lab11/monjolo/hardware/blast/rev_a/blast_pcb.png

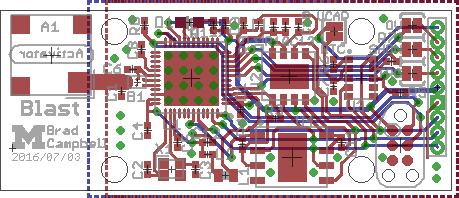
hardware/blast/rev_a/blast_pcb.png
