lab11/monjolo/hardware/breeze/rev_a/breeze_pcb.png

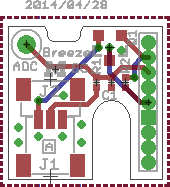
hardware/breeze/rev_a/breeze_pcb.png
