lab11/monjolo/hardware/cc_power_supply/rev_a/cc_power_supply_pcb.png

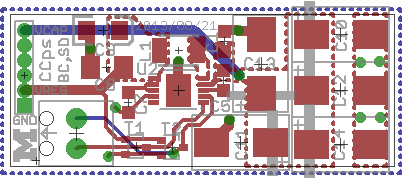
hardware/cc_power_supply/rev_a/cc_power_supply_pcb.png
