lab11/monjolo/hardware/coilcube/rev_c/coilcube_pcb.png

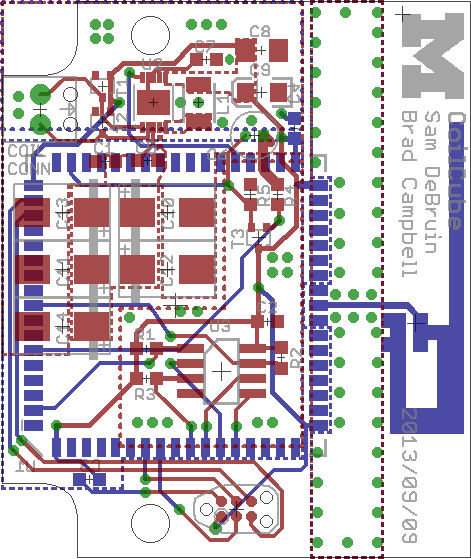
hardware/coilcube/rev_c/coilcube_pcb.png
