lab11/monjolo/hardware/impulse/rev_c/impulse_pcb.png

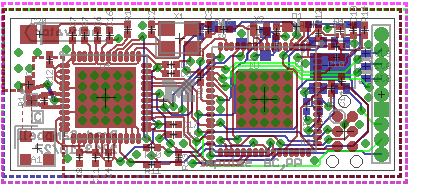
hardware/impulse/rev_c/impulse_pcb.png
