lab11/monjolo/hardware/sEHnsor/rev_a/sEHnsor.jpg

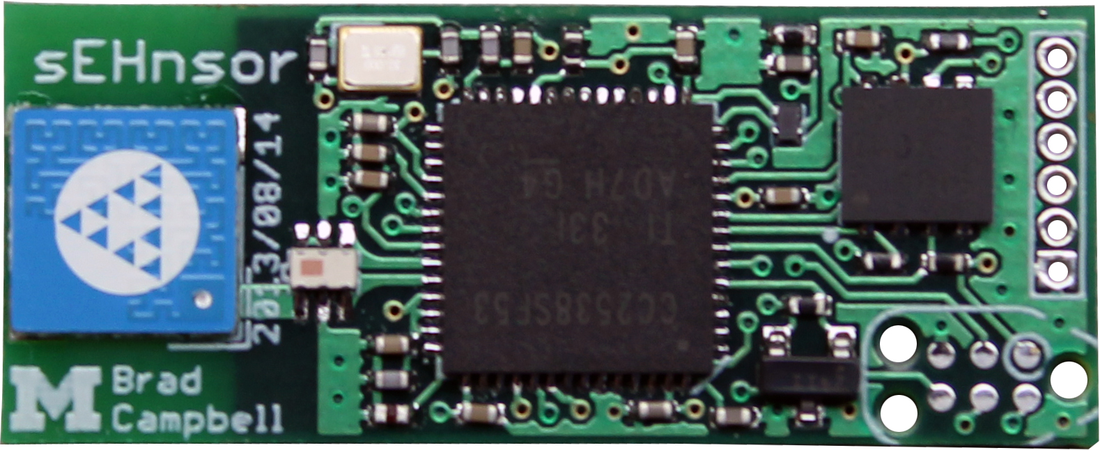
hardware/sEHnsor/rev_a/sEHnsor.jpg
