lab11/monjolo/hardware/sEHnsor/rev_a/sEHnsor_pcb.png

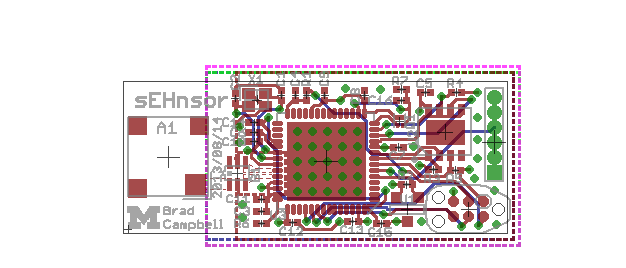
hardware/sEHnsor/rev_a/sEHnsor_pcb.png
