lab11/monjolo/media/blast_1000x405.jpg

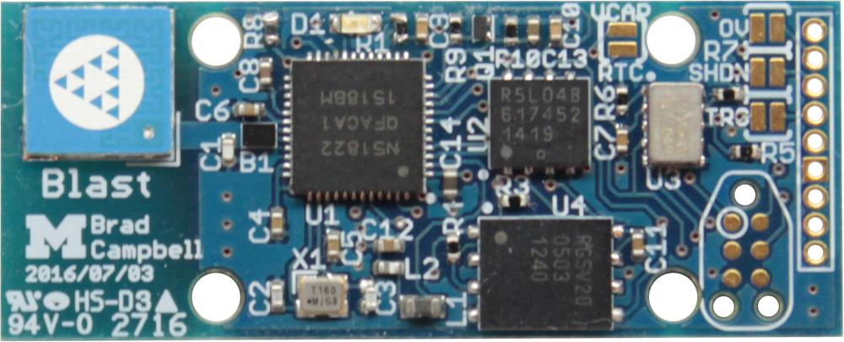
media/blast_1000x405.jpg
