lab11/monjolo/media/coilcube_case.jpg

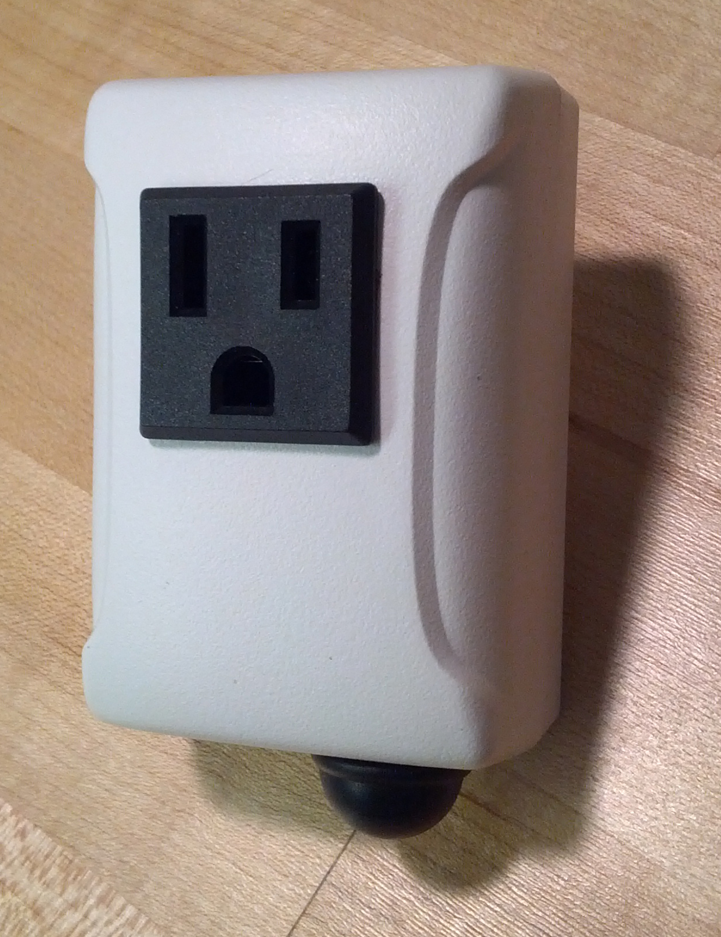
media/coilcube_case.jpg
