lab11/monjolo/media/coilcube_case_375x500.jpg

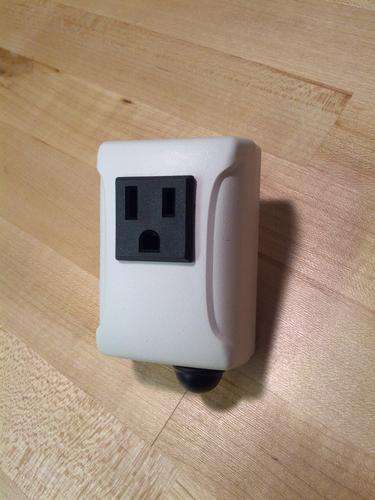
media/coilcube_case_375x500.jpg
