lab11/monjolo/media/coilcube_open.jpg

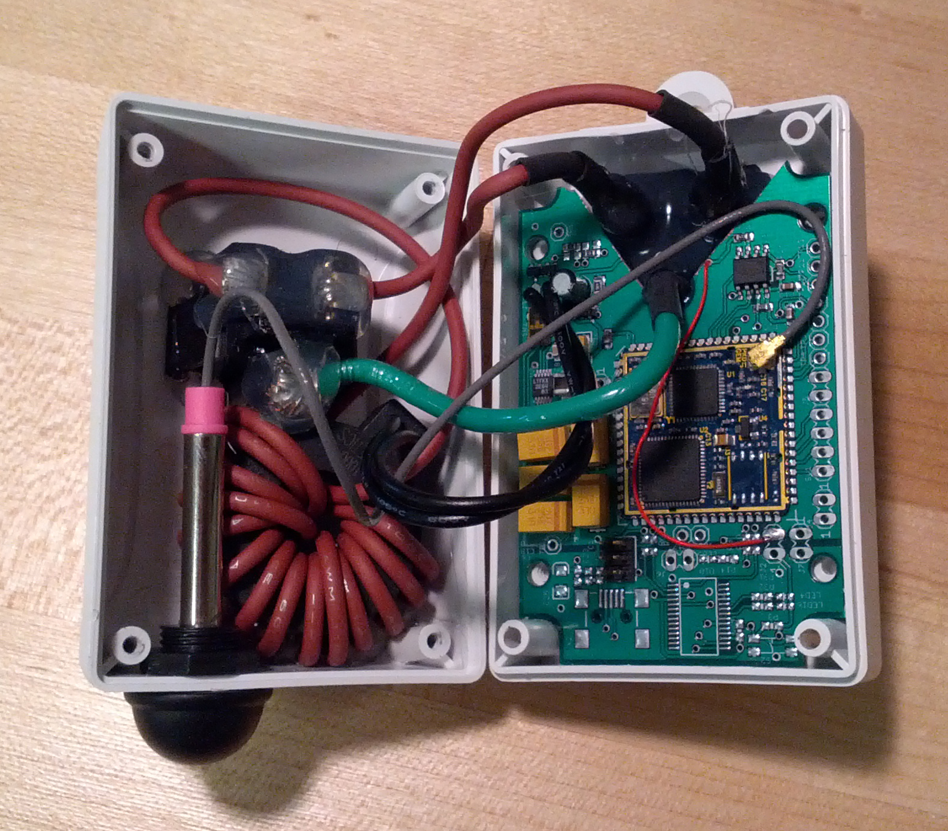
media/coilcube_open.jpg
