lab11/monjolo/media/coilcube_open_500x375.jpg

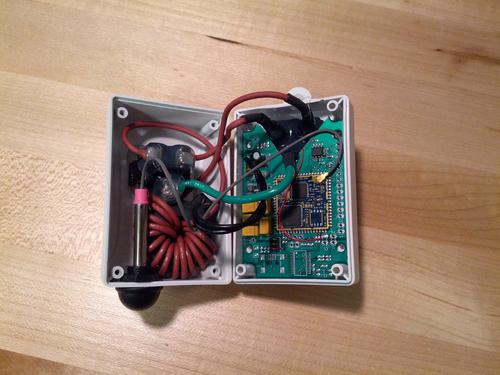
media/coilcube_open_500x375.jpg
