lab11/monjolo/media/coilcube_powerstrip.jpg

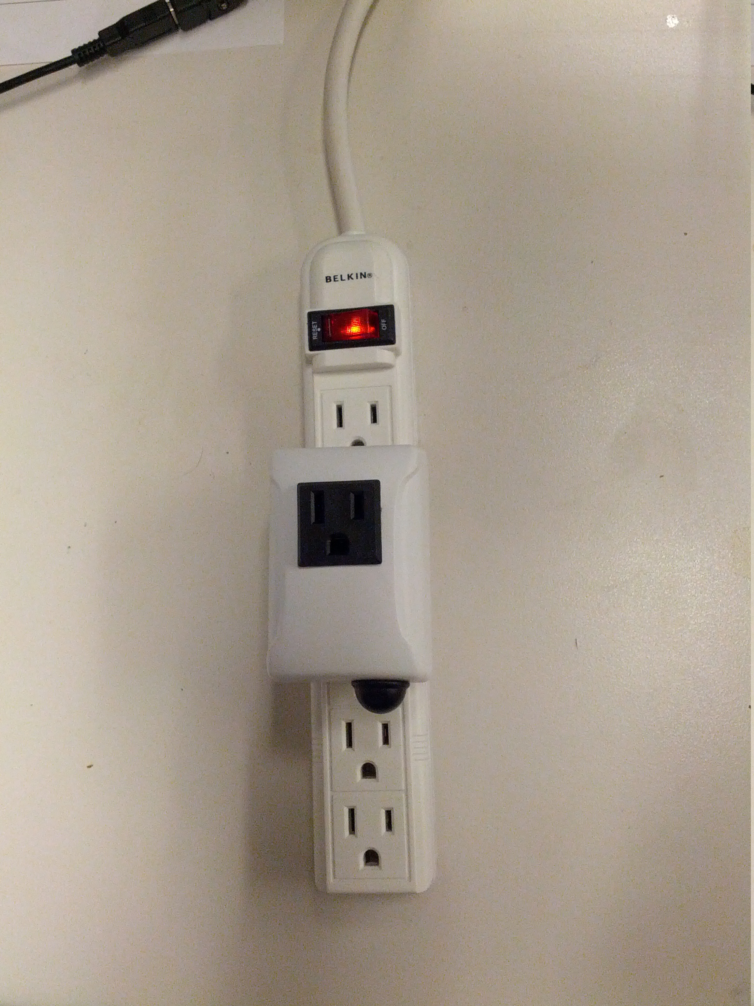
media/coilcube_powerstrip.jpg
