lab11/monjolo/media/gecko_power_supply_top_300x121.jpg

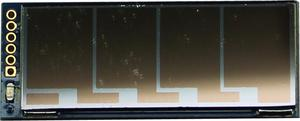
media/gecko_power_supply_top_300x121.jpg
