lab11/monjolo/media/ligeiro_1000x562.jpg

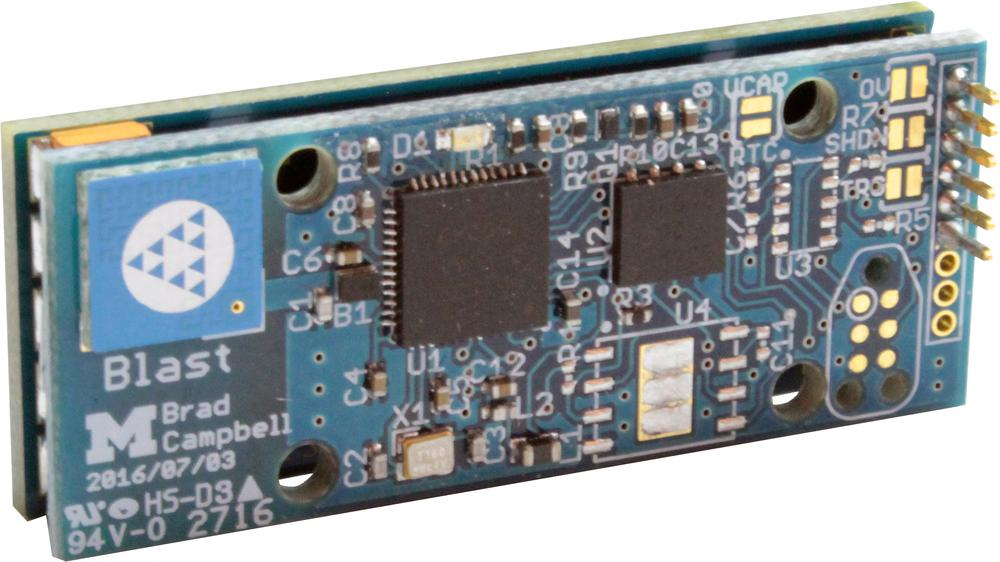
media/ligeiro_1000x562.jpg
