lab11/monjolo/media/ligeiro_case_alone_1000x724.jpg

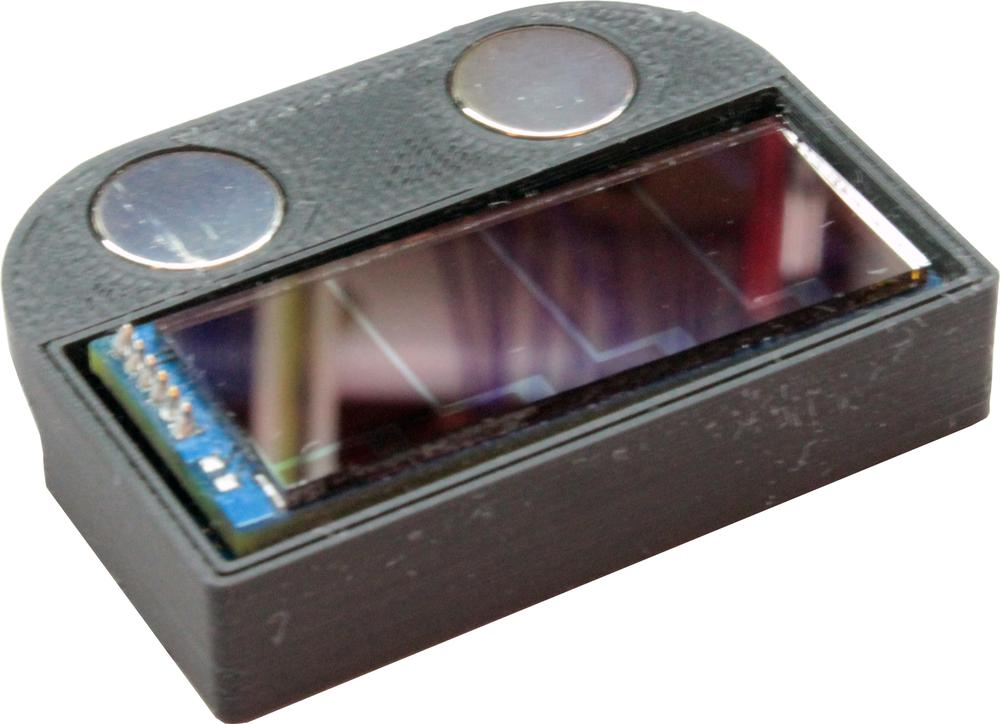
media/ligeiro_case_alone_1000x724.jpg
