lab11/monjolo/media/ligeiro_in_case_1000x1000.jpg

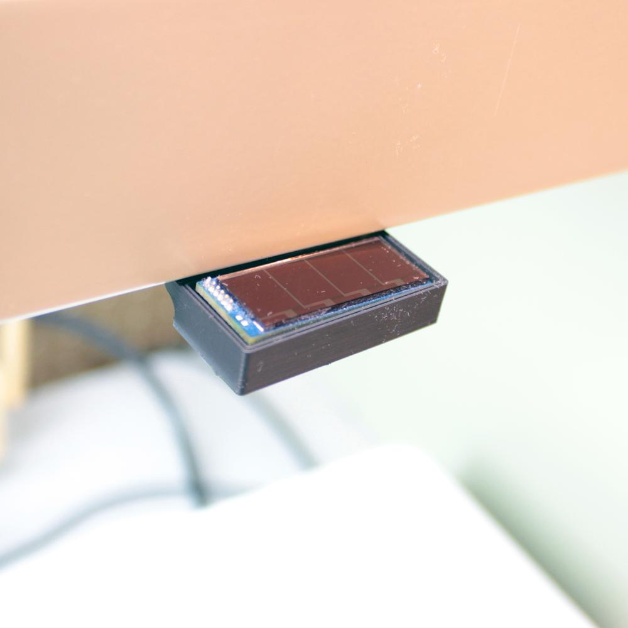
media/ligeiro_in_case_1000x1000.jpg
