lab11/monjolo/media/ligeiro_in_case_thin_1000x354.jpg

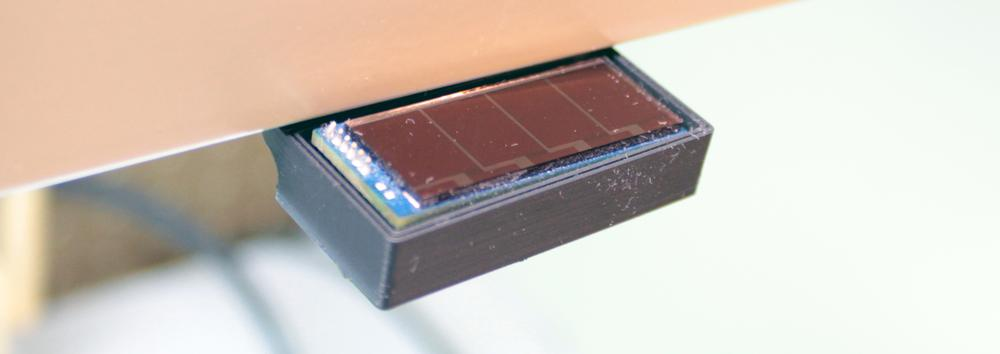
media/ligeiro_in_case_thin_1000x354.jpg
