lab11/monjolo/hardware/coilcube/rev_a/coilcube.pdf

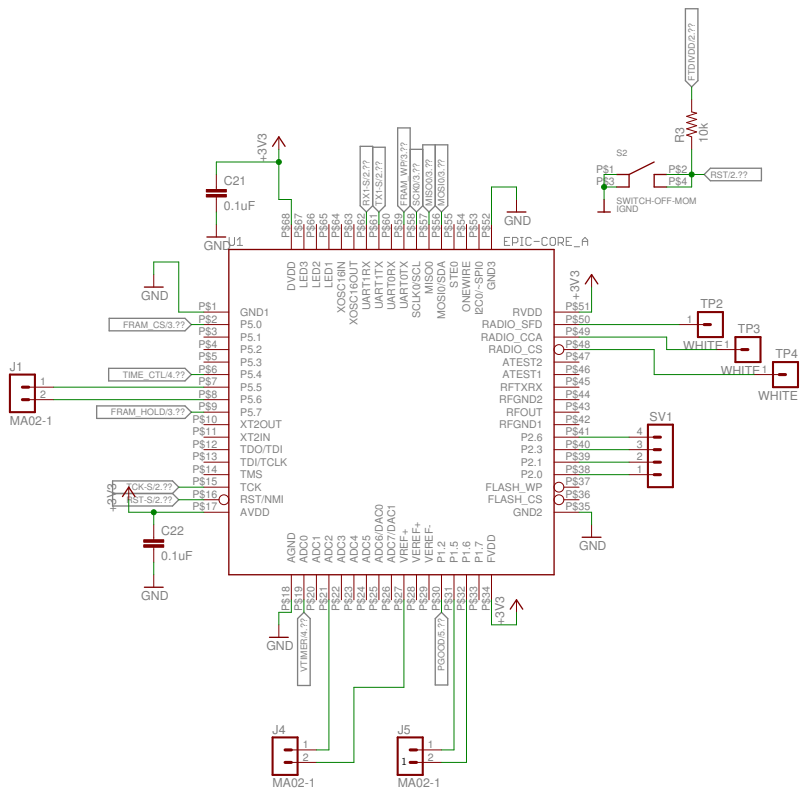
[picture p187: page 1]

C1 P$26 VREF+ P$27 VEREF+ P$28 VEREF- P$29 P1.2 P$30 P1.5 P$31 P1.6 P$32 P1.7 P$33 FVDD

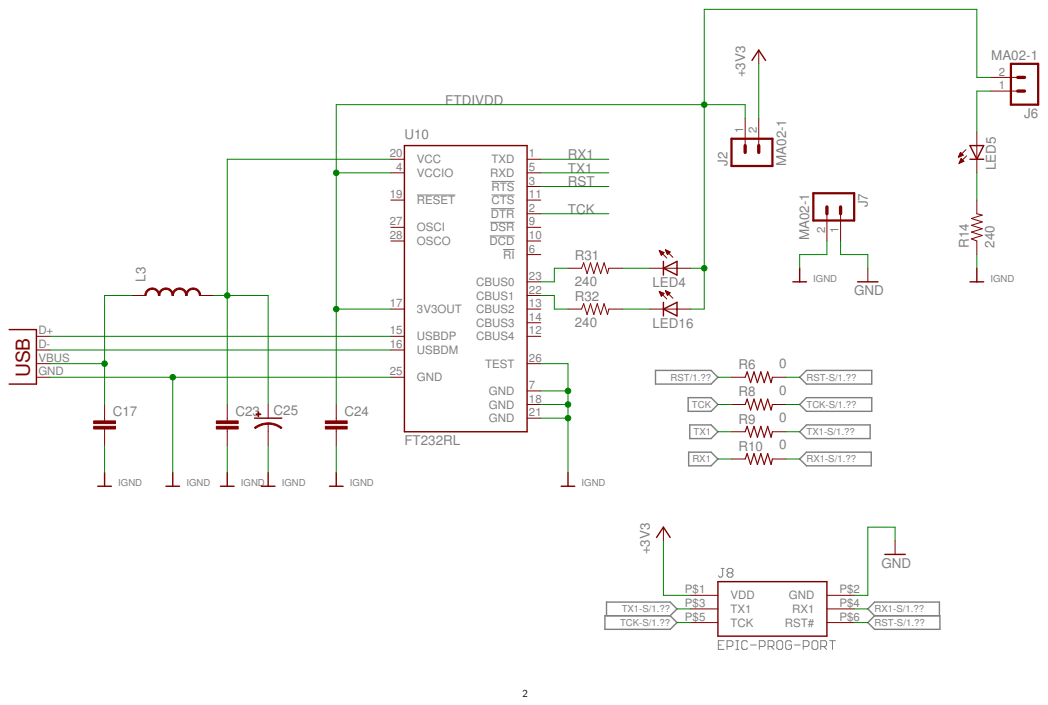
[picture p188: page 2]

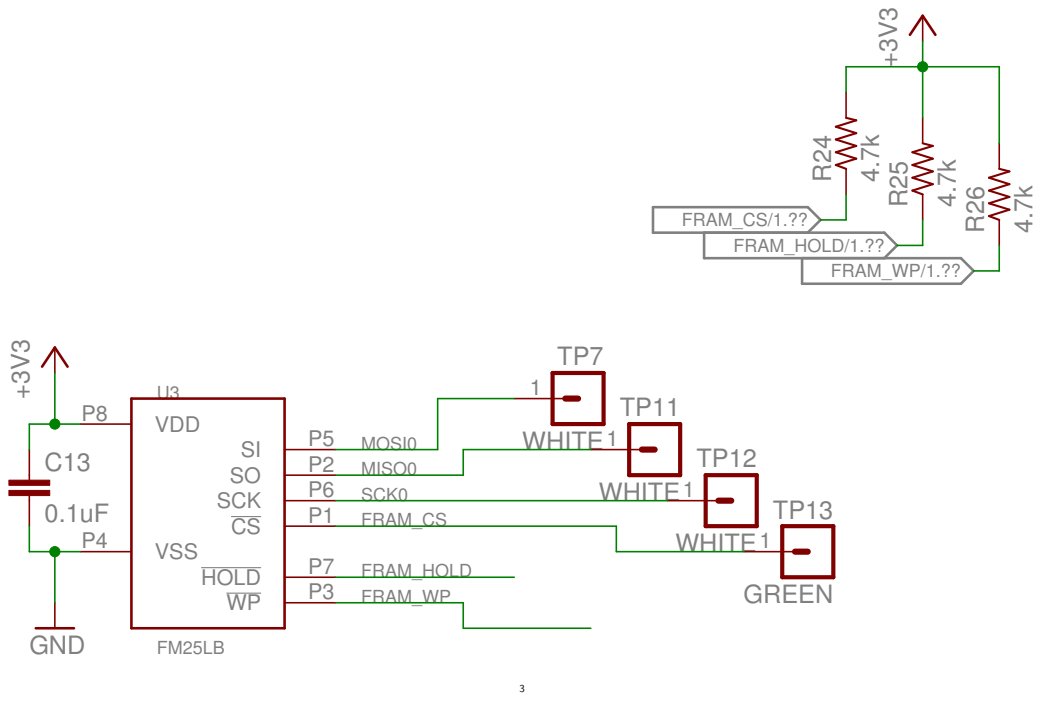
[picture p189: page 3]

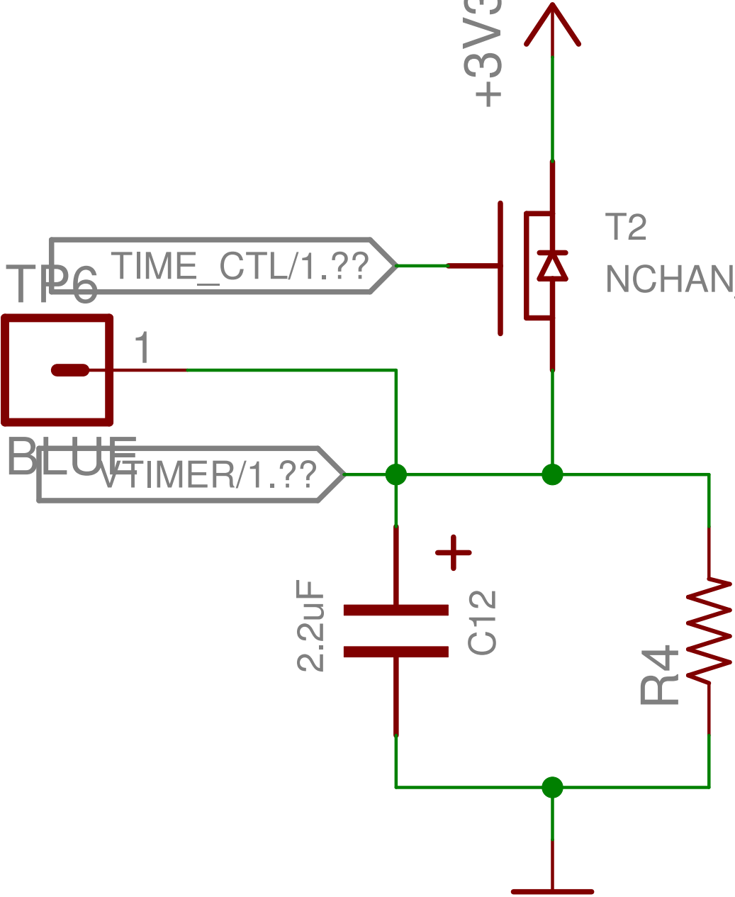
[picture p190: figure]
BLUE; VTIMER/1.??; TIME_CTL/1.??

4.7

M

# GND

# NCHAN_MOSFET

3

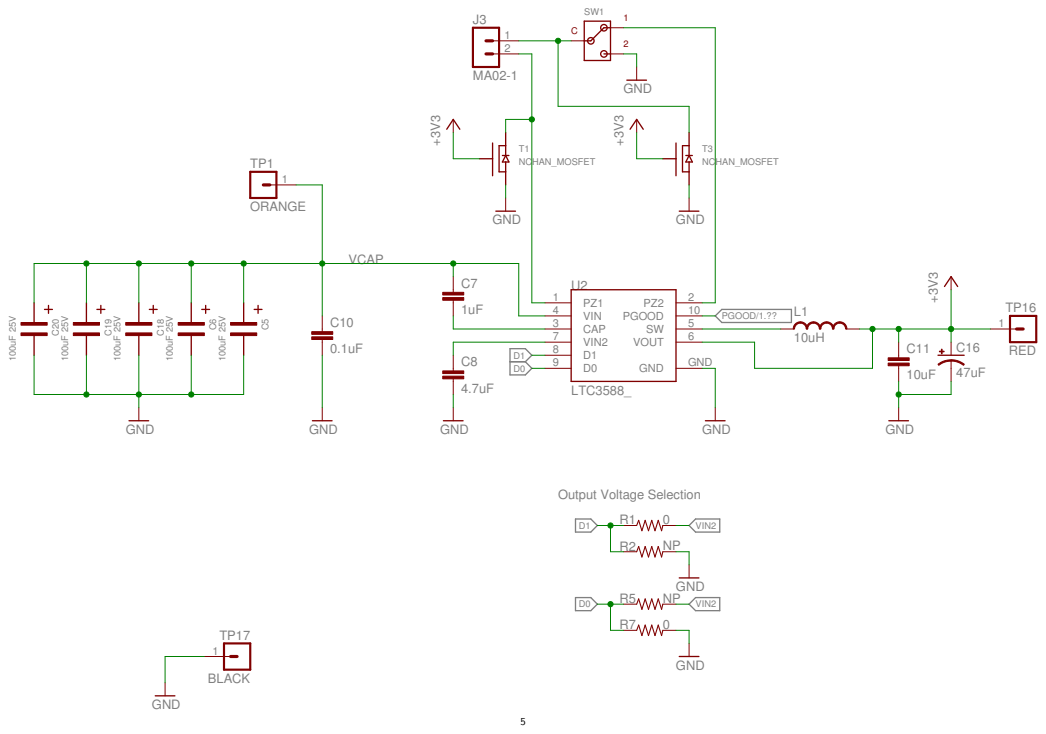
[picture p191: page 5]

Top and Bottom Layers 6 | 1 1 | 1 1 | 1 | 1 4 ¹ | 1

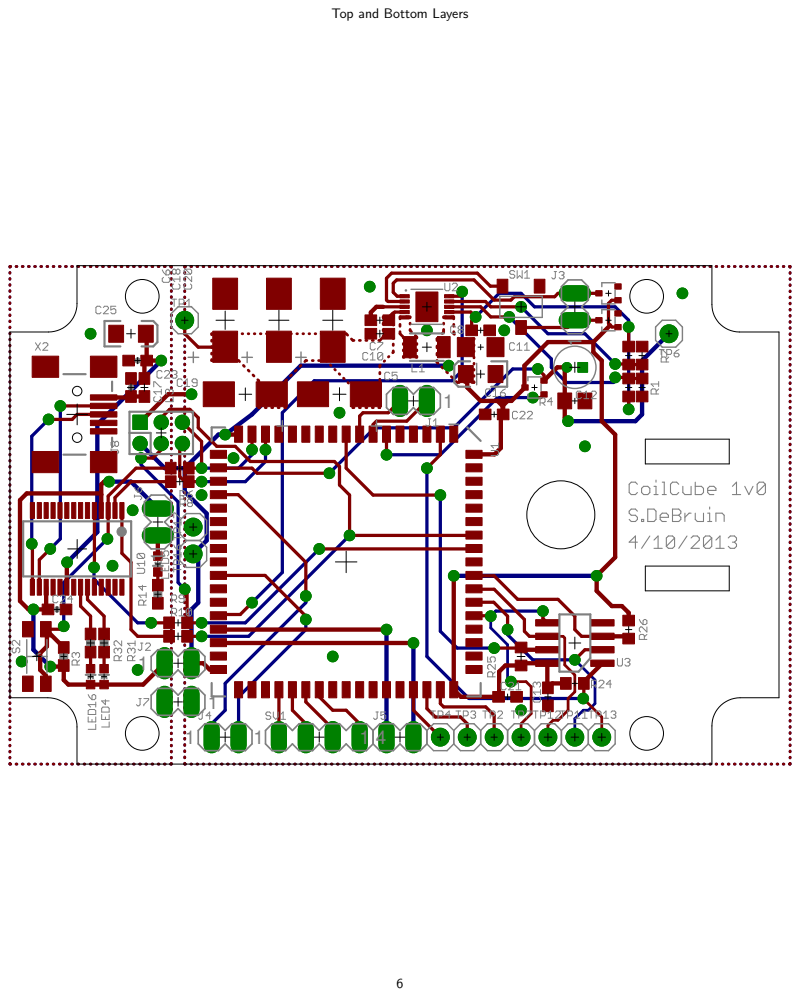
[picture p192: page 6]

Top Layer 7 | 1 1 | 1 1 | 1 | 1 4 ¹ | 1

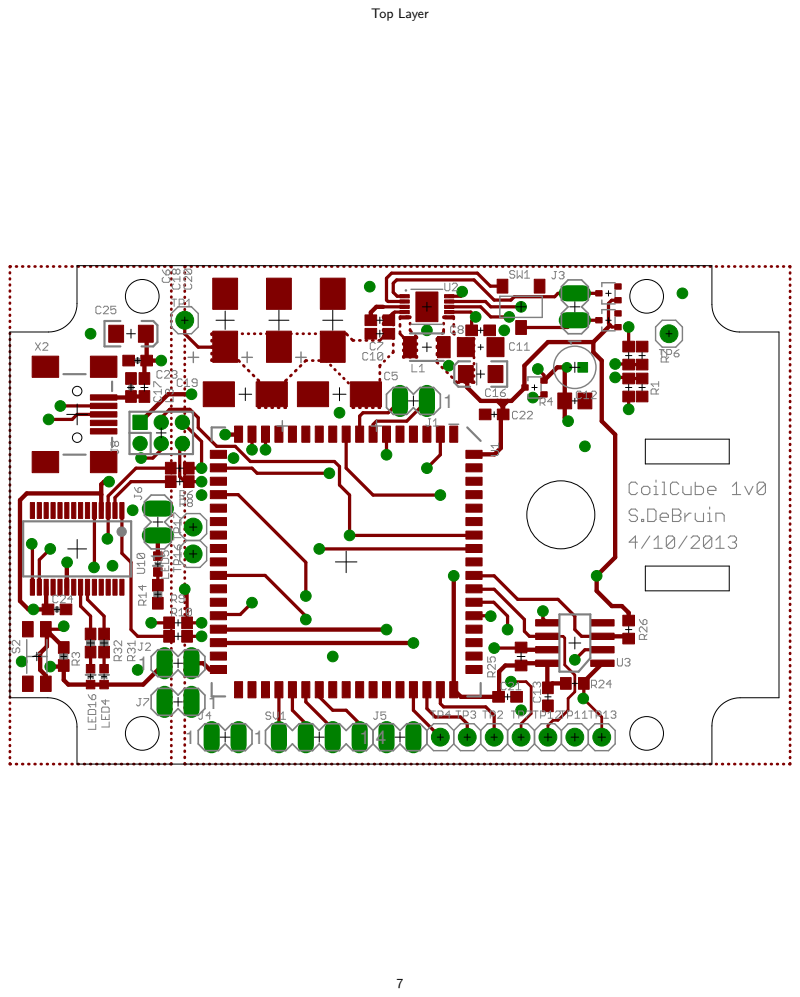
[picture p193: page 7]

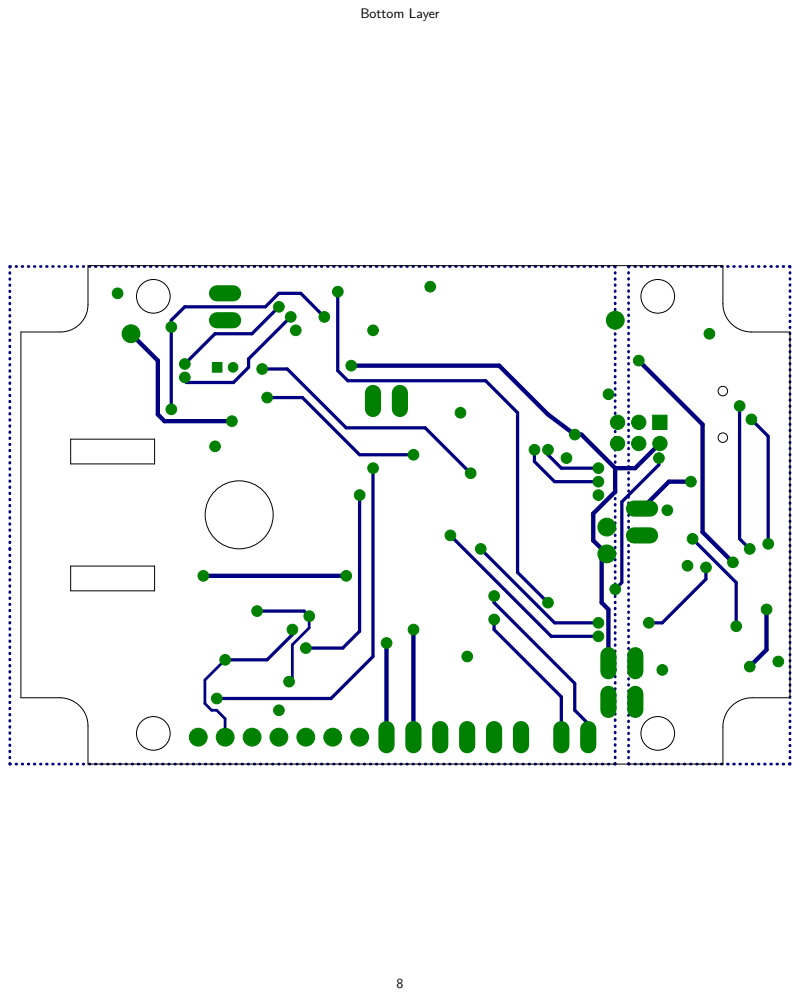
[picture p194: page 8]
Bottom Layer

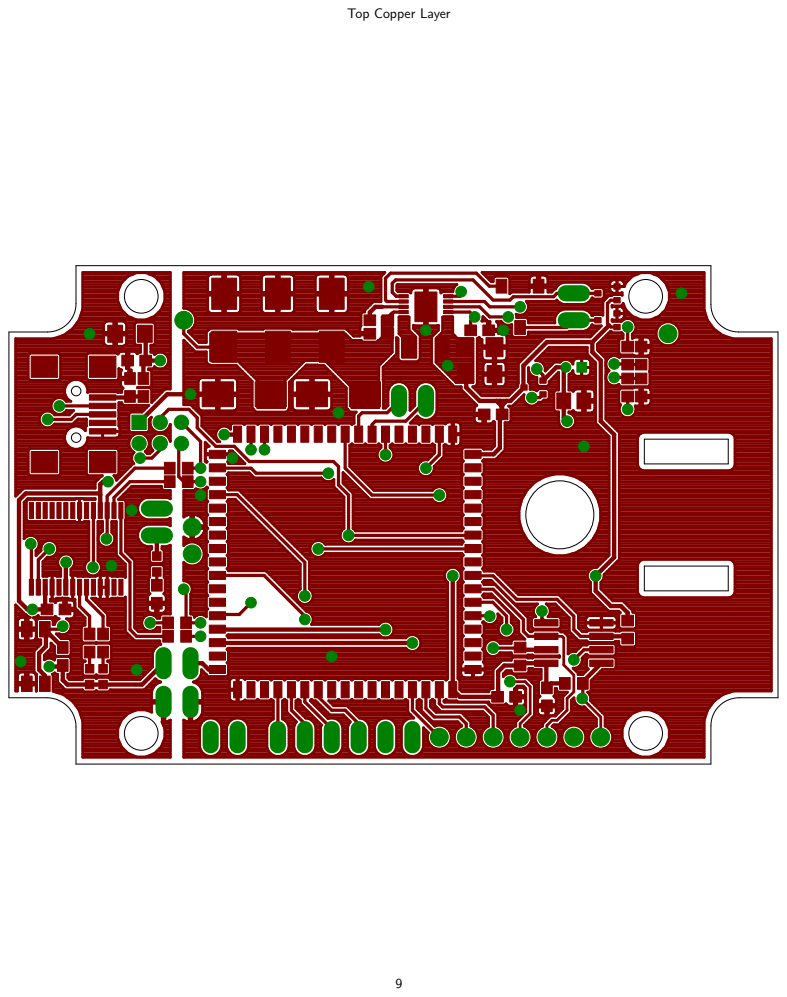
[picture p195: page 9]

Top Copper Layer

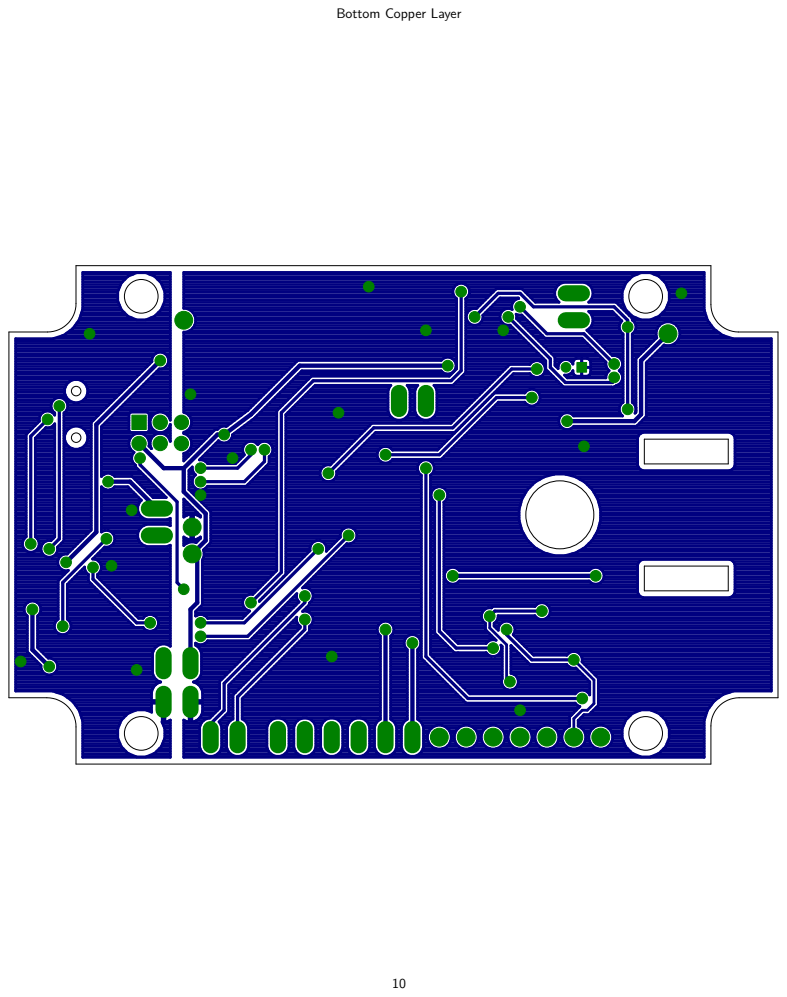
[picture p196: page 10]

Bottom Copper Layer

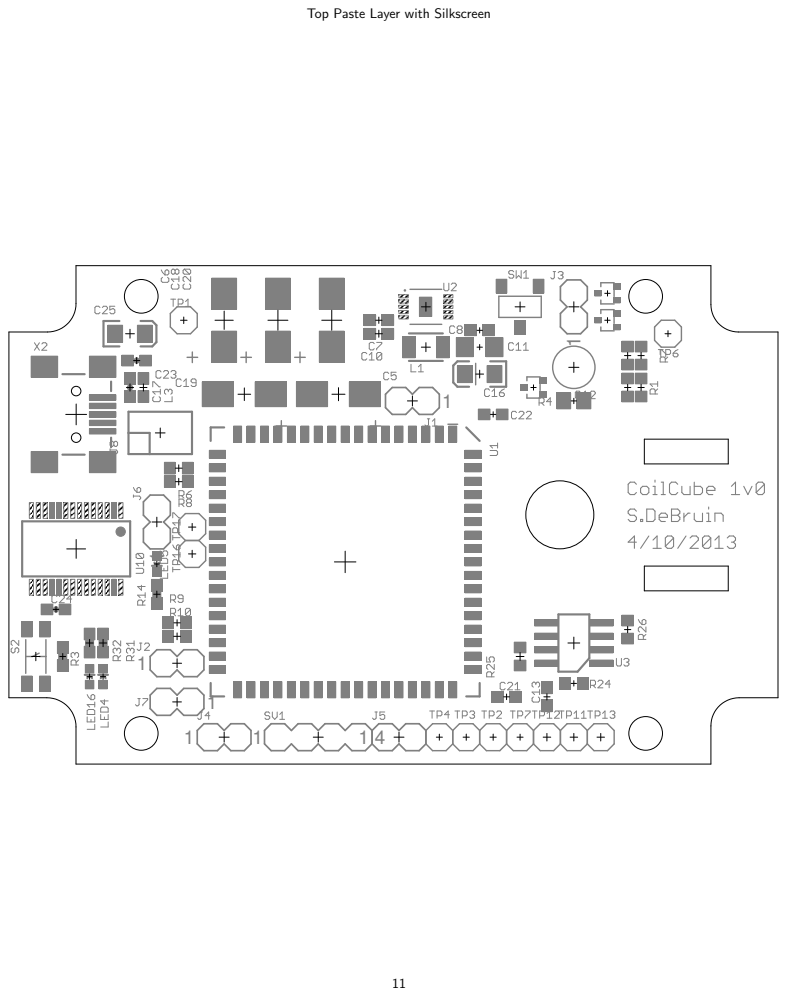
[picture p197: page 11]

Top Paste Layer with Silkscreen

Bottom Paste Layer with Silkscreen

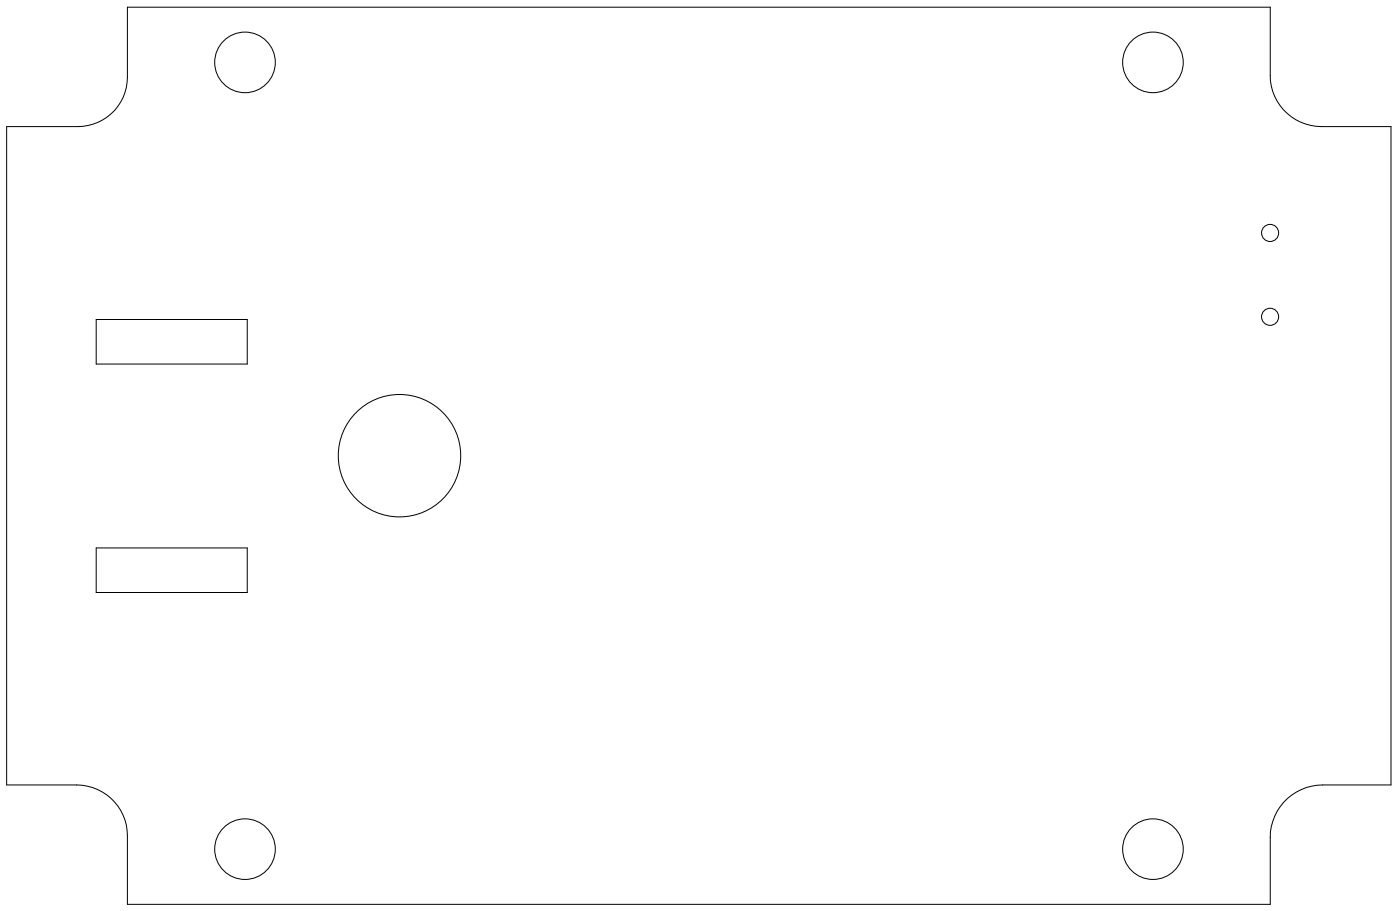
[picture p198: figure]
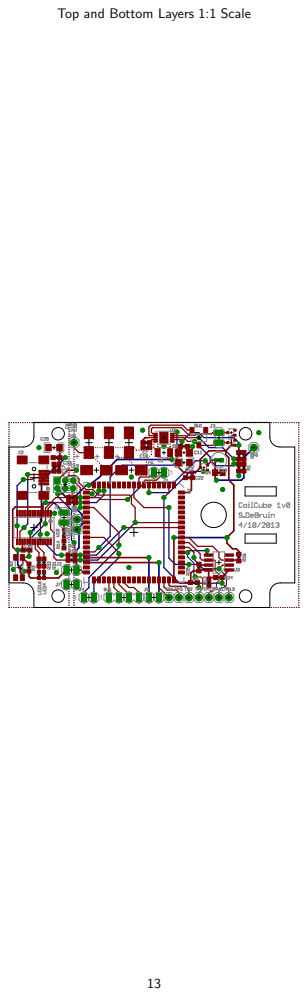
[picture p199: page 13]

Top and Bottom Layers 1:1 Scale

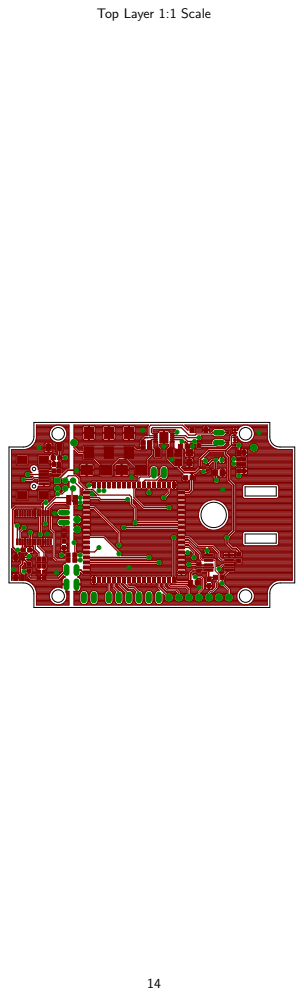
[picture p200: page 14]

Top Layer 1:1 Scale

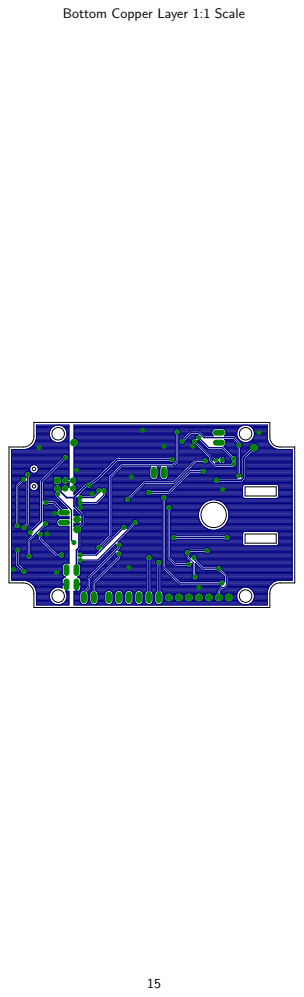
[picture p201: page 15]

Bottom Copper Layer 1:1 Scale
