lab11/monjolo/hardware/gecko_power_supply/rev_d/monjolo_d.brd

## EAGLE design hardware/gecko_power_supply/rev_d/monjolo_d.brd (2013-11-26, an earlier design)

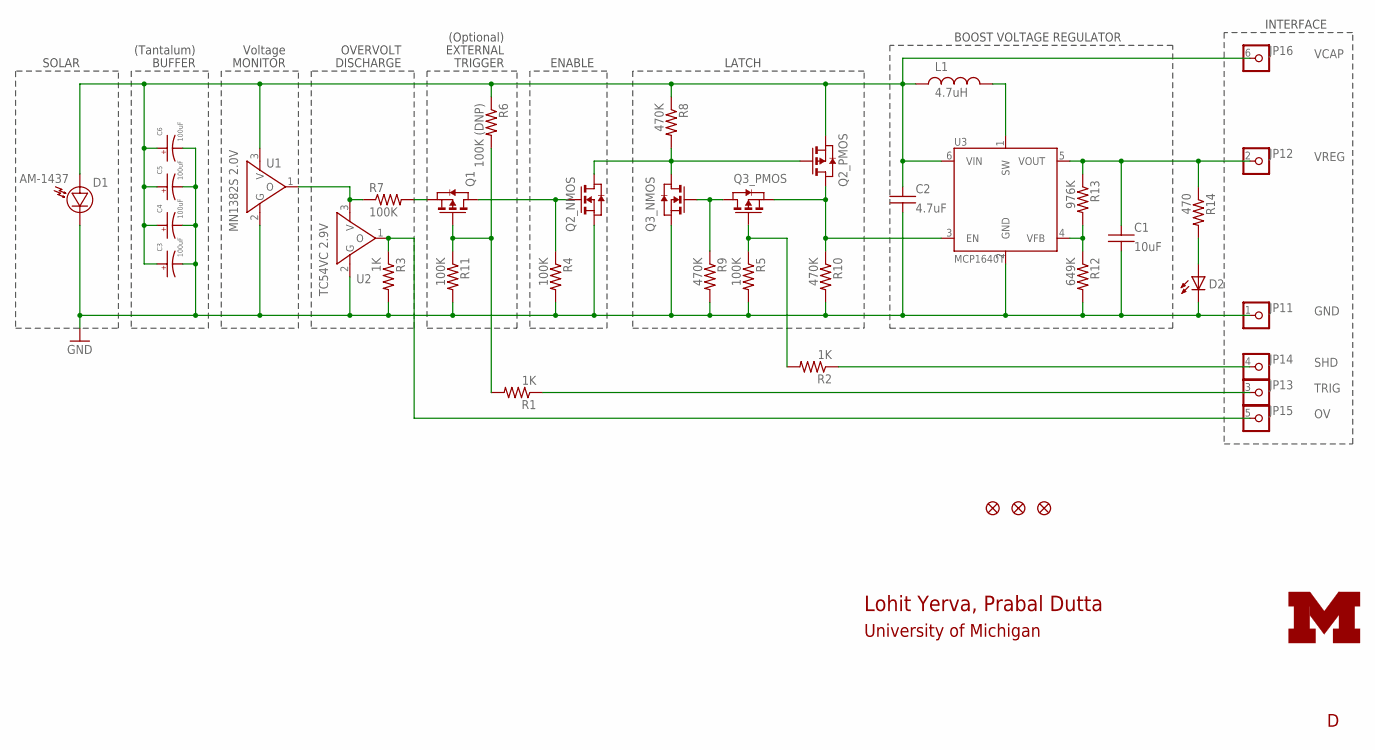
[picture p237: schematic monjolo_d.sch]

Parts:
C1: 10uF; R0603B
C2: 4.7uF; R0603B
C3, C4, C5, C6: 100uF; CAP1210
D1: AM-1437
D2: LED0603; LED-0603
JP1: PINHD6; HD6
JP2, JP3, JP4: FIDUCIAL1X2; FIDUCIAL-1X2
L1: 4.7uH; L2828
Q1: PMOSSOT23; SOT-23
Q2, Q3: DUAL_MOSFET_NP; TSOP-6
R1, R2, R3: 1K; R0603B
R4, R5, R7, R11: 100K; R0603B
R6: 100K (DNP); R0603B
R8, R9, R10: 470K; R0603B
R12: 649K; R0603B
R13: 976K; R0603B
R14: 470; R0603B
U1: MN1382S 2.0V; MINI-3DC
U2: TC54VC 2.9V; MINI-3DC
U3: MCP1640T; SOT-23-6
U$1: UMICH_SOLID_SMALL; UMICH_SOLID_75MIL

Connections:
GND: C1.2, C2.2, C3.ANODE, C4.ANODE, C5.ANODE, C6.ANODE, D1.- (C), D2.C, JP1.1, Q2.5 (S), Q3.5 (S), R3.2, R4.2, R5.2, R9.2, R10.2, R11.2, R12.2, U1.2 (G), U2.2 (G), U3.2 (GND)
unnamed: R12.1, R13.2, U3.4 (VFB)
unnamed: Q1.2 (S), R7.2
unnamed: JP1.3, R1.1
unnamed: L1.2, U3.1 (SW)
unnamed: D2.A, R14.2
unnamed: Q3.1 (G), Q3.4 (D), R9.1
unnamed: Q1.1 (D), Q2.1 (G), R4.1
unnamed: JP1.4, R2.1
unnamed: Q2.3 (G), Q2.6 (D), Q3.6 (D), R8.2
unnamed: Q3.3 (G), R2.2, R5.1
unnamed: JP1.5, R3.1, U2.1 (O)
unnamed: R7.1, U1.1 (O), U2.3 (V)
unnamed: Q1.3 (G), R1.2, R6.2, R11.1
unnamed: Q2.4 (D), Q3.2 (S), R10.1, U3.3 (EN)
VCAP: C2.1, C3.CATHODE, C4.CATHODE, C5.CATHODE, C6.CATHODE, D1.+ (A), JP1.6, L1.1, Q2.2 (S), R6.1, R8.1, U1.3 (V), U3.6 (VIN)
VREG: C1.1, JP1.2, R13.1, R14.1, U3.5 (VOUT)

Notes on the sheet:
Lohit Yerva, Prabal Dutta
VCAP
VREG
GND
SHD
TRIG
University of Michigan
SOLAR
(Tantalum)
BUFFER
Voltage
MONITOR
OVERVOLT
DISCHARGE
EXTERNAL
TRIGGER
(Optional)
ENABLE
LATCH
BOOST VOLTAGE REGULATOR
INTERFACE

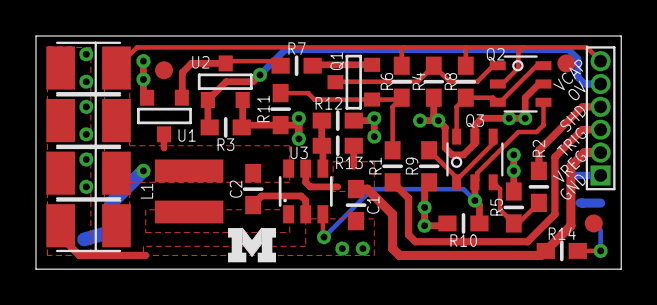
[picture p238: board monjolo_d.brd from above]

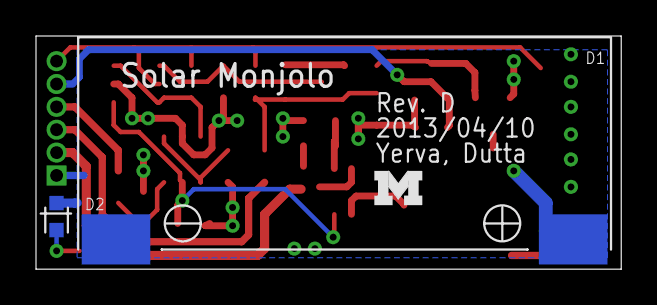
[picture p239: board monjolo_d.brd from below]

Board: 2 copper layers, 32.5 x 13.0 mm, 35 parts (3 on the bottom side), 17 nets.

Other parts of the board:
U$3: UMICH_SOLID_SMALL; UMICH_SOLID_75MIL
