lab11/monjolo/hardware/myth/rev_a/myth.brd

## EAGLE design hardware/myth/rev_a/myth.brd (2014-04-28)

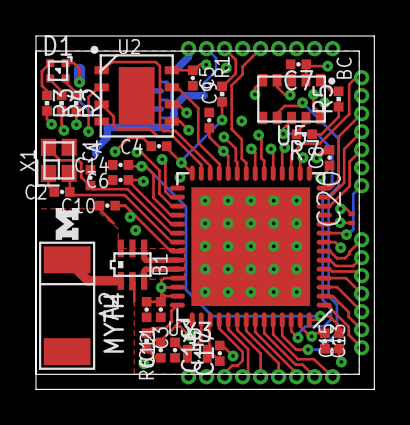
[picture p240: board myth.brd from above]

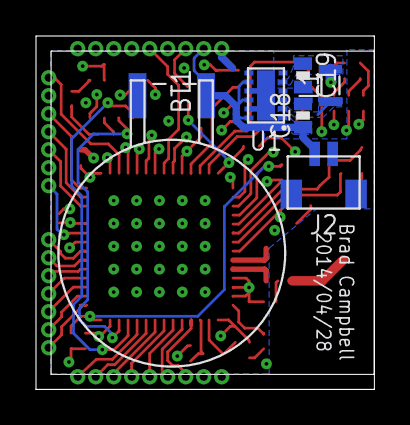
[picture p241: board myth.brd from below]

Board: 4 copper layers, 18.8 x 19.6 mm, 41 parts (6 on the bottom side), 55 nets.

Parts:
A2: FRACTUS-2.4GHZ-FR05-S1-N-0-102; FRACTUS-ANTENNA-FR05-S1-N-0-102
B1: 2450BM15A0002; 2450BM
BT1: ML-1220/F1AN; ML-1220/F1BN
C1, C2: 12pF; 0402_CAP
C3: 220pF; 0402_CAP
C4: 1nF; 0402_CAP
C5, C6, C8, C9, C10, C11, C12: 0.1uF; 0402_CAP
C7: 10nF; 0402_CAP
C13, C14, C15: 1uF; 0402_CAP
C16, C17: 22pF; 0402_CAP
C18, C19: 10uF; 0603_CAP
C20: 0.1uF; C0201
D1: SML-LX0404SIUPGUSB; 1MM_SQ_4PAD
J1: EPIC2-HEADER2
J2: SH_MALE_2/1MM; SH-1X2/1MM
L1: 2.2; MIPSZ201D
LOGO1: UMICH_SOLID_TINY; UMICH_SOLID_50MIL
R1: 2.2k; 0402_RES
R2, R3, R4: 1k; 0402_RES
R5, R7: 10k; 0402_RES
R6: 56k; 0402_RES
U1: TPS62740; R-PWSON-12
U2: FM25LBTDFN-8; TDFN-8
U3: CC2538; S-PVQFN-N56
U5: RV-3049-C3; MICRO-CRYSTAL-C3
X1: EPSON-FA-128; FA-128
X3: ABS05-32.768KHZ-T; ABS05

Connections:
!FRAM_CS: U2.1, U3.26
!FRAM_HOLD: U2.7, U3.25
!FRAM_WP: U2.3, U3.27
!RESET: J1.30, R1.1
!RTC_INT: U3.53, U5.7
ADC3: J1.25, U3.19
ADC4: J1.26, U3.20
ADC5: J1.27, U3.21
ADC6: J1.28, U3.22
ADC7: J1.29, U3.23
ANTENNA: A2.1, B1.1
B3: J1.9, U3.52
B4: J1.8, U3.51
B5: J1.7, U3.50
B6: J1.6, U3.49
BATTERY: BT1.POS, C18.1, J1.31, J2.2, U1.1, U1.8, U1.10, U1.12
BOOTLOADER_CTRL: J1.24, U3.18
BOOTLOADER_RX: J1.22, U3.16
BOOTLOADER_TX: J1.23, U3.17
C0: J1.21, U3.14
C1: J1.20, U3.13
C2: J1.19, U3.12
DGND_USB: J1.10, U3.1
DVDD_USB: J1.13, U3.4
GND: B1.2, B1.5, B1.6, BT1.NEG, C1.2, C2.2, C3.2, C4.2, C5.2, C6.2, C7.2, C8.2, C9.2, C10.2, C11.2, C12.2, C13.2, C14.2, C15.2, C16.2, C17.2, C18.2, C19.2, C20.2, J1.32, J2.1, R5.1, R6.2, R7.1, U1.3, U1.4, U1.9, U1.11, U1.NC, U2.4, U3.VSS_QFN, U5.6, X1.2, X1.4
I2C_SCL: J1.17, U3.9
I2C_SDA: J1.18, U3.8
LED_BLUE: R4.2, U3.30
LED_GREEN: R3.2, U3.31
LED_RED: R2.2, U3.29
unnamed: C4.1, R1.2, U3.28
unnamed: L1.1, U1.2
unnamed: C16.1, U3.44, X3.A
unnamed: D1.2, R2.1
unnamed: R6.1, U3.42
unnamed: C1.1, U3.34, X1.1
unnamed: C2.1, U3.35, X1.3
unnamed: D1.4, R3.1
unnamed: D1.3, R4.1
unnamed: C17.1, U3.45, X3.B
unnamed: R7.2, U5.9
unnamed: C14.1, C15.1, U3.32, U3.56
unnamed: R5.2, U5.1
RF_N: B1.3, U3.38
RF_P: B1.4, U3.37
RTC_CE: U3.54, U5.8
SPI_MISO: J1.14, U2.2, U3.5, U5.5
SPI_MOSI: J1.15, U2.5, U3.6, U5.10
SPI_SCK: J1.16, U2.6, U3.7, U5.4
TCK: J1.4, U3.47
TDO: J1.5, U3.48
TMS: J1.3, U3.46
USB_N: J1.12, U3.3
USB_P: J1.11, U3.2
VCC: C3.1, C5.1, C6.1, C7.1, C8.1, C9.1, C10.1, C11.1, C12.1, C13.1, C19.1, C20.1, D1.1, J1.1, L1.2, U1.5, U2.8, U3.10, U3.15, U3.24, U3.33, U3.36, U3.39, U3.40, U3.41, U3.43, U3.55, U5.2
