lab11/monjolo/hardware/bigben/rev_a/bigben.sch

## EAGLE design hardware/bigben/rev_a/bigben.sch (2014-05-19)

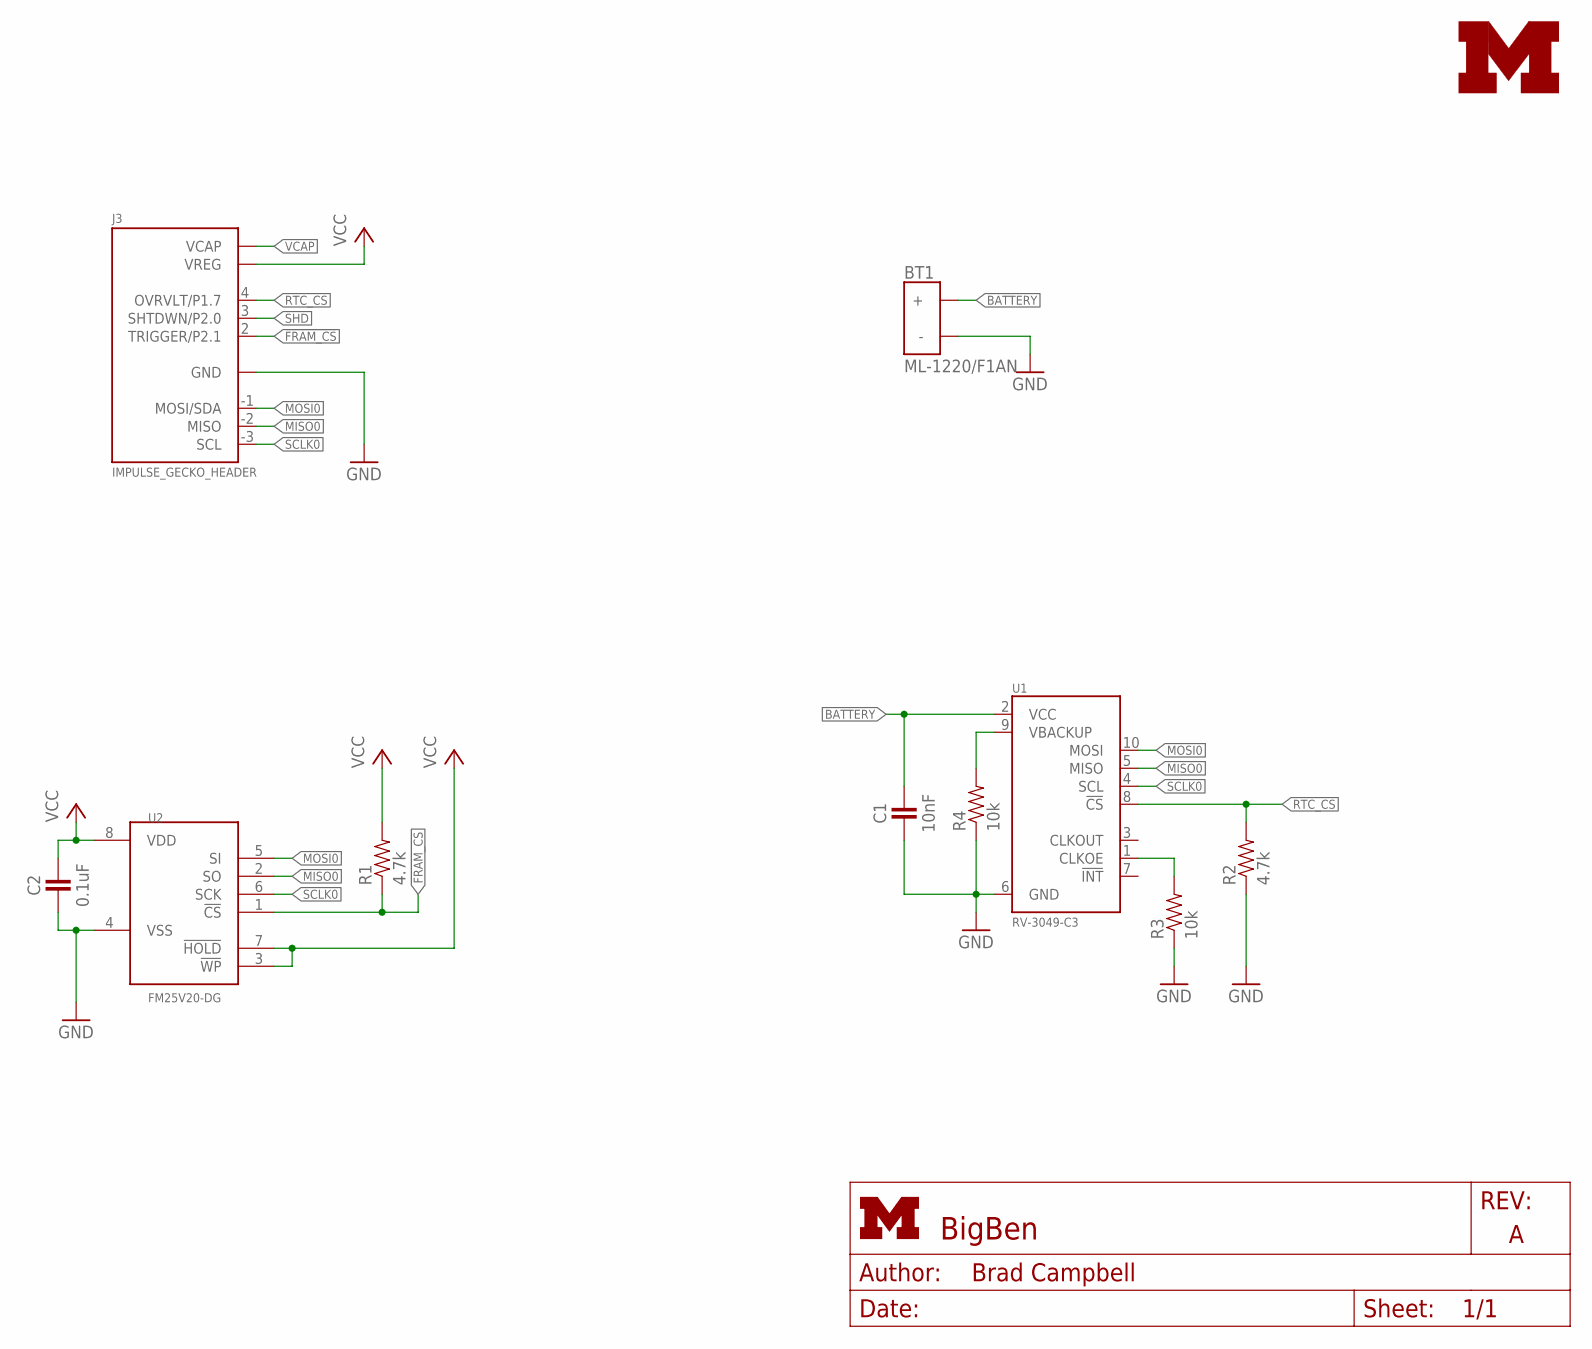
[picture p242: schematic bigben.sch]

Parts:
BT1: ML-1220/F1AN; ML-1220/F1BN
C1: 10nF; 0402_CAP
C2: 0.1uF; 0402_CAP
J3: IMPULSE_GECKO_HEADER; HEADER1X9/0.05IN
LOGO1: UMICH_SOLID_TINY; UMICH_SOLID_50MIL
R1, R2: 4.7k; 0402_RES
R3, R4: 10k; 0402_RES
U1: RV-3049-C3; MICRO-CRYSTAL-C3
U2: FM25V20-DG; TDFN-8/6MM

Connections:
!FRAM_CS: J3.2 (TRIGGER/P2.1), R1.1, U2.1 (!CS)
BATTERY: BT1.POS (+), C1.1, U1.2 (VCC)
GND: BT1.NEG (-), C1.2, C2.2, J3.0 (GND), R2.1, R3.1, R4.1, U1.6 (GND), U2.4 (VSS)
MISO0: J3.-2 (MISO), U1.5 (MISO), U2.2 (SO)
MOSI0: J3.-1 (MOSI/SDA), U1.10 (MOSI), U2.5 (SI)
unnamed: R4.2, U1.9 (VBACKUP)
unnamed: R3.2, U1.1 (CLKOE)
RTC_CS: J3.4 (OVRVLT/P1.7), R2.2, U1.8 (!CS)
SCLK0: J3.-3 (SCL), U1.4 (SCL), U2.6 (SCK)
SHD: J3.3 (SHTDWN/P2.0)
VCAP: J3.5 (VCAP)
VCC: C2.1, J3.1 (VREG), R1.2, U2.3 (!WP), U2.7 (!HOLD), U2.8 (VDD)
