lab11/monjolo/hardware/epic2/rev_a/epic2.sch

## EAGLE design hardware/epic2/rev_a/epic2.sch (2014-03-24)

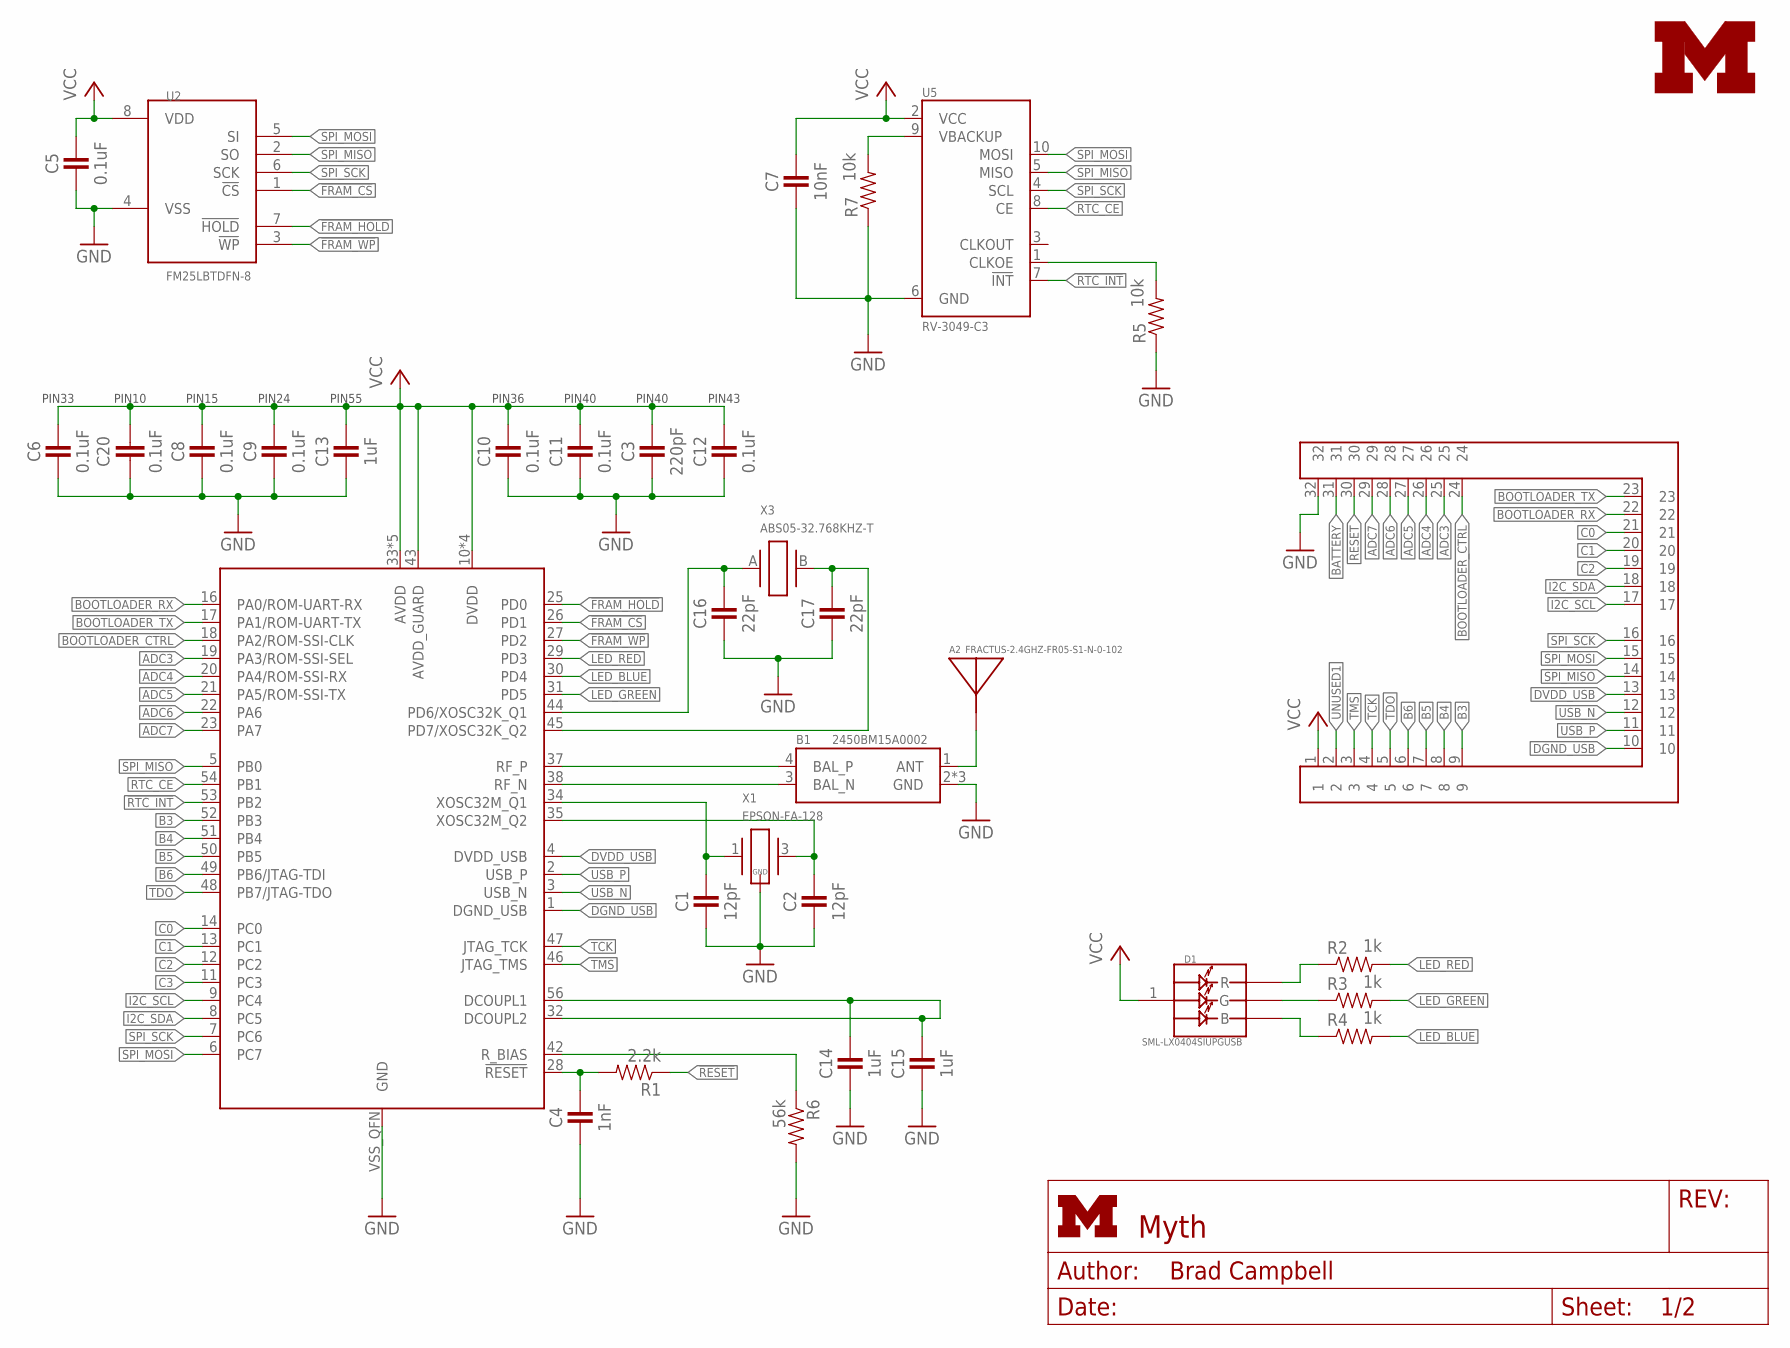
[picture p243: schematic epic2.sch, sheet 1]

Parts:
A2: FRACTUS-2.4GHZ-FR05-S1-N-0-102; FRACTUS-ANTENNA-FR05-S1-N-0-102
B1: 2450BM15A0002; 2450BM
C1, C2: 12pF; 0402_CAP
C3: 220pF; 0402_CAP
C4: 1nF; 0402_CAP
C5, C6, C8, C9, C10, C11, C12: 0.1uF; 0402_CAP
C7: 10nF; 0402_CAP
C13, C14, C15: 1uF; 0402_CAP
C16, C17: 22pF; 0402_CAP
C20: 0.1uF; C0201
D1: SML-LX0404SIUPGUSB; 1MM_SQ_4PAD
J1: EPIC2-HEADER2
LOGO1: UMICH_SOLID_TINY; UMICH_SOLID_50MIL
R1: 2.2k; 0402_RES
R2, R3, R4: 1k; 0402_RES
R5, R7: 10k; 0402_RES
R6: 56k; 0402_RES
U2: FM25LBTDFN-8; TDFN-8; DIGIKEY FM25L04B-DGRA-ND
U3: CC2538; S-PVQFN-N56
U5: RV-3049-C3; MICRO-CRYSTAL-C3
X1: EPSON-FA-128; FA-128
X3: ABS05-32.768KHZ-T; ABS05

Connections:
!FRAM_CS: U2.1 (!CS), U3.26 (PD1)
!FRAM_HOLD: U2.7 (!HOLD), U3.25 (PD0)
!FRAM_WP: U2.3 (!WP), U3.27 (PD2)
!RESET: J1.30, R1.1
!RTC_INT: U3.53 (PB2), U5.7 (!INT)
ADC3: J1.25, U3.19 (PA3/ROM-SSI-SEL)
ADC4: J1.26, U3.20 (PA4/ROM-SSI-RX)
ADC5: J1.27, U3.21 (PA5/ROM-SSI-TX)
ADC6: J1.28, U3.22 (PA6)
ADC7: J1.29, U3.23 (PA7)
ANTENNA: A2.1, B1.1 (ANT)
B3: J1.9, U3.52 (PB3)
B4: J1.8, U3.51 (PB4)
B5: J1.7, U3.50 (PB5)
B6: J1.6, U3.49 (PB6/JTAG-TDI)
BATTERY: J1.31
BOOTLOADER_CTRL: J1.24, U3.18 (PA2/ROM-SSI-CLK)
BOOTLOADER_RX: J1.22, U3.16 (PA0/ROM-UART-RX)
BOOTLOADER_TX: J1.23, U3.17 (PA1/ROM-UART-TX)
C0: J1.21, U3.14 (PC0)
C1: J1.20, U3.13 (PC1)
C2: J1.19, U3.12 (PC2)
C3: U3.11 (PC3)
DGND_USB: J1.10, U3.1 (DGND_USB)
DVDD_USB: J1.13, U3.4 (DVDD_USB)
GND: B1.2 (GND), C1.2, C2.2, C3.2, C4.2, C5.2, C6.2, C7.2, C8.2, C9.2, C10.2, C11.2, C12.2, C13.2, C14.2, C15.2, C16.2, C17.2, C20.2, J1.32, R5.1, R6.2, R7.1, U2.4 (VSS), U3.VSS_QFN (GND), U5.6 (GND), X1.2 (GND)
I2C_SCL: J1.17, U3.9 (PC4)
I2C_SDA: J1.18, U3.8 (PC5)
LED_BLUE: R4.2, U3.30 (PD4)
LED_GREEN: R3.2, U3.31 (PD5)
LED_RED: R2.2, U3.29 (PD3)
unnamed: C4.1, R1.2, U3.28 (!RESET)
unnamed: C16.1, U3.44 (PD6/XOSC32K_Q1), X3.A (1)
unnamed: D1.2 (R), R2.1
unnamed: R6.1, U3.42 (R_BIAS)
unnamed: C1.1, U3.34 (XOSC32M_Q1), X1.1
unnamed: C2.1, U3.35 (XOSC32M_Q2), X1.3 (2)
unnamed: D1.4 (G), R3.1
unnamed: D1.3 (B), R4.1
unnamed: C17.1, U3.45 (PD7/XOSC32K_Q2), X3.B (2)
unnamed: R7.2, U5.9 (VBACKUP)
unnamed: C14.1, C15.1, U3.32 (DCOUPL2), U3.56 (DCOUPL1)
unnamed: R5.2, U5.1 (CLKOE)
RF_N: B1.3 (BAL_N), U3.38 (RF_N)
RF_P: B1.4 (BAL_P), U3.37 (RF_P)
RTC_CE: U3.54 (PB1), U5.8 (CE)
SPI_MISO: J1.14, U2.2 (SO), U3.5 (PB0), U5.5 (MISO)
SPI_MOSI: J1.15, U2.5 (SI), U3.6 (PC7), U5.10 (MOSI)
SPI_SCK: J1.16, U2.6 (SCK), U3.7 (PC6), U5.4 (SCL)
TCK: J1.4, U3.47 (JTAG_TCK)
TDO: J1.5, U3.48 (PB7/JTAG-TDO)
TMS: J1.3, U3.46 (JTAG_TMS)
UNUSED1: J1.2
USB_N: J1.12, U3.3 (USB_N)
USB_P: J1.11, U3.2 (USB_P)
VCC: C3.1, C5.1, C6.1, C7.1, C8.1, C9.1, C10.1, C11.1, C12.1, C13.1, C20.1, D1.1 (VDD), J1.1, U2.8 (VDD), U3.10 (DVDD), U3.33 (AVDD), U3.43 (AVDD_GUARD), U5.2 (VCC)

Notes on the sheet:
PIN10
PIN15
PIN24
PIN55
PIN33
PIN36
PIN40
PIN43

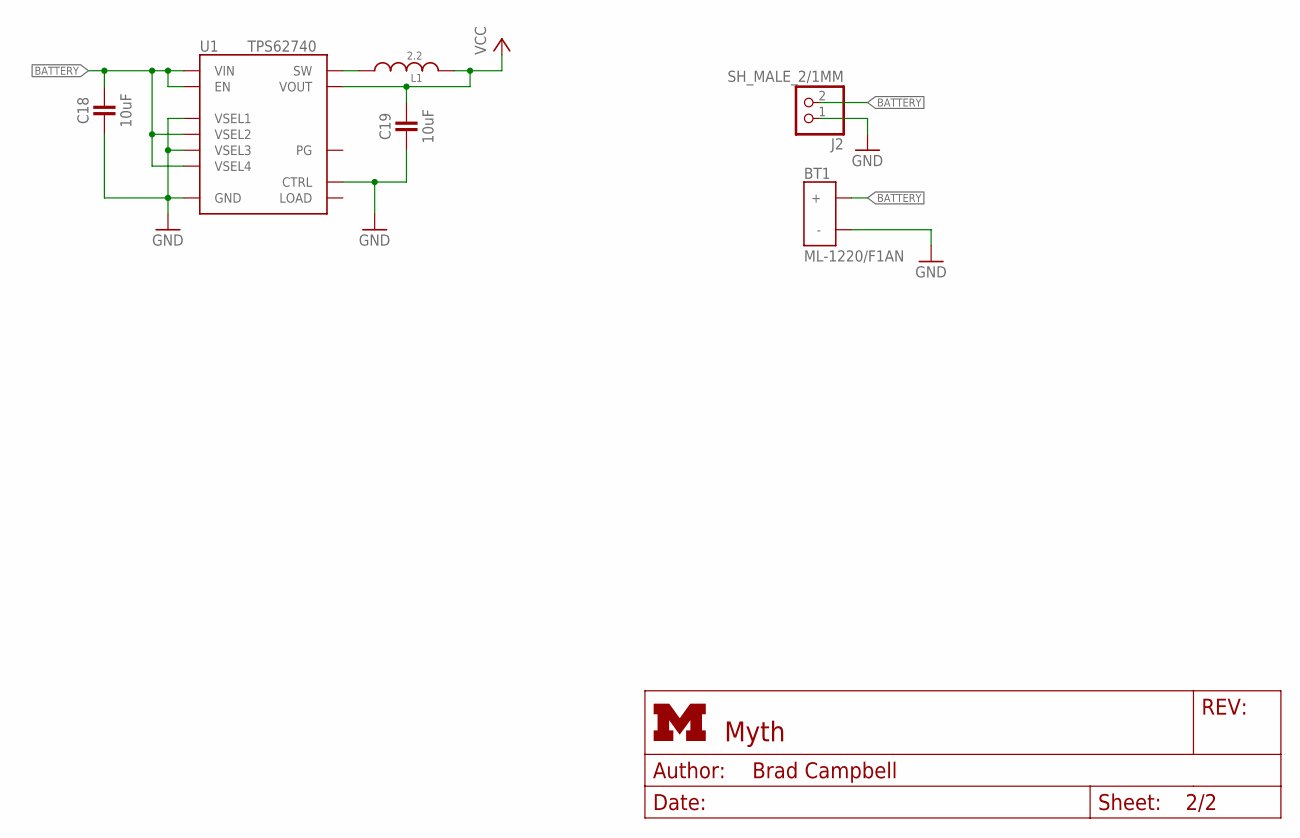
[picture p244: schematic epic2.sch, sheet 2]

Parts:
BT1: ML-1220/F1AN; ML-1220/F1BN
C18: 10uF; 0603_CAP; DIGIKEY 490-7316-1-ND
C19: 10uF; 0603_CAP; DIGIKEY 1276-1119-1-ND
J2: SH_MALE_2/1MM; SH-1X2/1MM
L1: 2.2; MIPSZ201D
U1: TPS62740; R-PWSON-12

Connections:
BATTERY: BT1.POS (+), C18.1, J2.2, U1.1 (VIN), U1.8 (VSEL4), U1.10 (VSEL2), U1.12 (EN)
GND: BT1.NEG (-), C18.2, C19.2, J2.1, U1.3 (GND), U1.4 (CTRL), U1.9 (VSEL3), U1.11 (VSEL1)
unnamed: L1.1, U1.2 (SW)
VCC: C19.1, L1.2, U1.5 (VOUT)
