lab11/monjolo/contiki/platform/sehnsor/dev/board.h

/** \addtogroup cc2538
 * @{
 *
 * \defgroup sEHnsor
 *
 * \note   Do not include this file directly. It gets included by contiki-conf
 *         after all relevant directives have been set.
 */
#ifndef BOARD_H_
#define BOARD_H_

#include "dev/gpio.h"
#include "dev/nvic.h"
/*---------------------------------------------------------------------------*/
/** \name SmartRF LED configuration
 *
 * LEDs on the SmartRF06 (EB and BB) are connected as follows:
 * - LED1 (Red)    -> PC0
 * - LED2 (Yellow) -> PC1
 * - LED3 (Green)  -> PC2
 * - LED4 (Orange) -> PC3
 *
 * LED1 shares the same pin with the USB pullup
 * @{
 */
/*---------------------------------------------------------------------------*/
/* Some files include leds.h before us, so we need to get rid of defaults in
 * leds.h before we provide correct definitions */
#undef LEDS_GREEN
#undef LEDS_YELLOW
#undef LEDS_RED
#undef LEDS_CONF_ALL

/* Notify various examples that we do not have LEDs */
#define PLATFORM_HAS_LEDS        0
/** @} */
/*---------------------------------------------------------------------------*/
/** \name USB configuration
 *
 * The USB pullup is driven by PC0 and is shared with LED1
 */
#define USB_PULLUP_PORT          GPIO_C_BASE
#define USB_PULLUP_PIN           0
#define USB_PULLUP_PIN_MASK      (1 << USB_PULLUP_PIN)
/** @} */
/*---------------------------------------------------------------------------*/
/** \name UART configuration
 *
 * On the SmartRF06EB, the UART (XDS back channel) is connected to the
 * following ports/pins
 * - RX:  PA0
 * - TX:  PA1
 * - CTS: PB0 (Can only be used with UART1)
 * - RTS: PD3 (Can only be used with UART1)
 *
 * We configure the port to use UART0. To use UART1, change UART_CONF_BASE
 * @{
 */
#define UART_CONF_BASE           UART_0_BASE

#define UART_RX_PORT             GPIO_A_NUM
#define UART_RX_PIN              0

#define UART_TX_PORT             GPIO_A_NUM
#define UART_TX_PIN              1

#define UART_CTS_PORT            GPIO_B_NUM
#define UART_CTS_PIN             0

#define UART_RTS_PORT            GPIO_D_NUM
#define UART_RTS_PIN             3
/** @} */
/*---------------------------------------------------------------------------*/
/* Notify various examples that we do not have buttons */
#define PLATFORM_HAS_BUTTON      0
/** @} */
/*---------------------------------------------------------------------------*/
/**
 * \name Device string used on startup
 * @{
 */
#define BOARD_STRING "sEHnsor"
/** @} */

#endif /* BOARD_H_ */

/**
 * @}
 * @}
 */
