lab11/monjolo/contiki/apps/SEHpacket/sehpacket.c

/*
 * Copyright (c) 2012, Texas Instruments Incorporated - http://www.ti.com/
 * All rights reserved.
 *
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
 * 3. Neither the name of the copyright holder nor the names of its
 *    contributors may be used to endorse or promote products derived
 *    from this software without specific prior written permission.
 *
 * THIS SOFTWARE IS PROVIDED BY THE COPYRIGHT HOLDERS AND CONTRIBUTORS
 * ``AS IS'' AND ANY EXPRESS OR IMPLIED WARRANTIES, INCLUDING, BUT NOT
 * LIMITED TO, THE IMPLIED WARRANTIES OF MERCHANTABILITY AND FITNESS
 * FOR A PARTICULAR PURPOSE ARE DISCLAIMED.  IN NO EVENT SHALL THE
 * COPYRIGHT HOLDER OR CONTRIBUTORS BE LIABLE FOR ANY DIRECT, INDIRECT,
 * INCIDENTAL, SPECIAL, EXEMPLARY, OR CONSEQUENTIAL DAMAGES
 * (INCLUDING, BUT NOT LIMITED TO, PROCUREMENT OF SUBSTITUTE GOODS OR
 * SERVICES; LOSS OF USE, DATA, OR PROFITS; OR BUSINESS INTERRUPTION)
 * HOWEVER CAUSED AND ON ANY THEORY OF LIABILITY, WHETHER IN CONTRACT,
 * STRICT LIABILITY, OR TORT (INCLUDING NEGLIGENCE OR OTHERWISE)
 * ARISING IN ANY WAY OUT OF THE USE OF THIS SOFTWARE, EVEN IF ADVISED
 * OF THE POSSIBILITY OF SUCH DAMAGE.
 */
/**
 * \addtogroup cc2538
 * @{
 *
 * \defgroup cc2538-examples cc2538dk Example Projects
 * @{
 *
 * \defgroup cc2538-demo cc2538dk Demo Project
 *
 *   Example project demonstrating the cc2538dk functionality
 *
 *   This assumes that you are using a SmartRF06EB with a cc2538 EM
 *
 * - Boot sequence: LEDs flashing, LED2 followed by LED3 then LED4
 * - etimer/clock : Every LOOP_INTERVAL clock ticks the LED defined as
 *                  LEDS_PERIODIC will turn on
 * - rtimer       : Exactly LEDS_OFF_HYSTERISIS rtimer ticks later,
 *                  LEDS_PERIODIC will turn back off
 * - Buttons      :
 *                - BTN_DOWN turns on LEDS_REBOOT and causes a watchdog reboot
 *                - BTN_UP to soft reset (SYS_CTRL_PWRDBG::FORCE_WARM_RESET)
 *                - BTN_LEFT and BTN_RIGHT flash the LED defined as LEDS_BUTTON
 * - UART         : Every LOOP_INTERVAL the EM will print something over the
 *                  UART. Receiving an entire line of text over UART (ending
 *                  in \\r) will cause LEDS_SERIAL_IN to toggle
 * - Radio comms  : BTN_SELECT sends a rime broadcast. Reception of a rime
 *                  packet will toggle LEDs defined as LEDS_RF_RX
 *
 * @{
 *
 * \file
 *     Example demonstrating the cc2538dk platform
 */
#include "coilcube_ip.h"
#include "contiki.h"
#include "cpu.h"
#include "sys/etimer.h"
#include "sys/rtimer.h"
#include "dev/leds.h"
#include "dev/uart.h"
#include "dev/button-sensor.h"
#include "dev/watchdog.h"
#include "dev/serial-line.h"
#include "dev/sys-ctrl.h"
#include "net/rime/broadcast.h"
#include "net/uip.h"
#include "net/uip-udp-packet.h"
#include "net/uiplib.h"
#include "net/uip-ds6-route.h"
#include "net/uip-ds6-nbr.h"

#include <stdio.h>
#include <stdint.h>
/*---------------------------------------------------------------------------*/
#define LOOP_INTERVAL       CLOCK_SECOND
#define LEDS_OFF_HYSTERISIS (RTIMER_SECOND >> 1)
#define LEDS_PERIODIC       LEDS_YELLOW
#define LEDS_BUTTON         LEDS_RED
#define LEDS_SERIAL_IN      LEDS_ORANGE
#define LEDS_REBOOT         LEDS_ALL
#define LEDS_RF_RX          (LEDS_YELLOW | LEDS_ORANGE)
#define BROADCAST_CHANNEL   129
/*---------------------------------------------------------------------------*/
#define MACDEBUG 0

#define DEBUG 1
#if DEBUG
#include <stdio.h>
#define PRINTF(...) printf(__VA_ARGS__)
#define PRINT6ADDR(addr) PRINTF(" %02x%02x:%02x%02x:%02x%02x:%02x%02x:%02x%02x:%02x%02x:%02x%02x:%02x%02x ", ((uint8_t *)addr)[0], ((uint8_t *)addr)[1], ((uint8_t *)addr)[2], ((uint8_t *)addr)[3], ((uint8_t *)addr)[4], ((uint8_t *)addr)[5], ((uint8_t *)addr)[6], ((uint8_t *)addr)[7], ((uint8_t *)addr)[8], ((uint8_t *)addr)[9], ((uint8_t *)addr)[10], ((uint8_t *)addr)[11], ((uint8_t *)addr)[12], ((uint8_t *)addr)[13], ((uint8_t *)addr)[14], ((uint8_t *)addr)[15])
#define PRINTLLADDR(lladdr) PRINTF(" %02x:%02x:%02x:%02x:%02x:%02x ",lladdr->addr[0], lladdr->addr[1], lladdr->addr[2], lladdr->addr[3],lladdr->addr[4], lladdr->addr[5])
#else
#define PRINTF(...)
#define PRINT6ADDR(addr)
#endif

#define PING6_NB 5
#define PING6_DATALEN 16

#define UIP_IP_BUF   ((struct uip_ip_hdr *)&uip_buf[UIP_LLH_LEN])
#define UIP_ICMP_BUF ((struct uip_icmp_hdr *)&uip_buf[uip_l2_l3_hdr_len])

static uip_ipaddr_t my_addr;
static uip_ipaddr_t dest_addr;
static uip_ipaddr_t bcast_ipaddr;
static uip_lladdr_t bcast_lladdr = {{0, 0, 0, 0, 0, 0, 0, 0}};
static struct uip_udp_conn *client_conn;

pkt_data_t pkt_data = {PROFILE_ID, SEHNSOR_VERSION, 0, 0};

static struct etimer periodic_timer;

PROCESS(ipv6_process, "IPv6 process");
AUTOSTART_PROCESSES(&ipv6_process);


static void
recv_handler(void)
{
  char *str;

  if (uip_newdata()) {
    str = uip_appdata;
    str[uip_datalen()] = '\0';
    printf("Response from the server: '%s'\n", str);
  }
}

/*---------------------------------------------------------------------------*/
static void
send_handler(process_event_t ev, process_data_t data)
{
  pkt_data.counter++;
  pkt_data.seq_no++;

  PRINTF("Sending UDP!!! packet\n");
  uip_udp_packet_send(client_conn, (uint8_t*) &pkt_data, sizeof(pkt_data_t));

  PRINTF("After sent udp packet.\n");
}

/*---------------------------------------------------------------------------*/
PROCESS_THREAD(ipv6_process, ev, data)
{


  PROCESS_BEGIN();

  // Set the local address
  uip_ip6addr(&my_addr, 0, 0, 0, 0, 0, 0, 0, 0);
  uip_ds6_set_addr_iid(&my_addr, &uip_lladdr);
  uip_ds6_addr_add(&my_addr, 0, ADDR_MANUAL);

  // Setup the destination address
  uiplib_ipaddrconv(RECEIVER_ADDR, &dest_addr);

  // Add a "neighbor" for our custom route
  // Setup the default broadcast route
  uiplib_ipaddrconv(ADDR_ALL_ROUTERS, &bcast_ipaddr);
  uip_ds6_nbr_add(&bcast_ipaddr, &bcast_lladdr, 0, NBR_REACHABLE);
  uip_ds6_route_add(&dest_addr, 128, &bcast_ipaddr);

  // Setup a udp "connection"
  client_conn = udp_new(&dest_addr, UIP_HTONS(RECEIVER_PORT), NULL);
  if (client_conn == NULL) {
    // Too many udp connections
    // not sure how to exit...stupid contiki
  }
  udp_bind(client_conn, UIP_HTONS(3001));

  etimer_set(&periodic_timer, 10*CLOCK_SECOND);

  while(1) {
    PROCESS_YIELD();

    if (etimer_expired(&periodic_timer)) {
      send_handler(ev, data);
      etimer_restart(&periodic_timer);
    } else if (ev == tcpip_event) {
      recv_handler();
    }
  }

  PROCESS_END();
}
/*---------------------------------------------------------------------------*/
